willtmakinen78/weatherclock/pics/IMG_20200605_103530.jpg

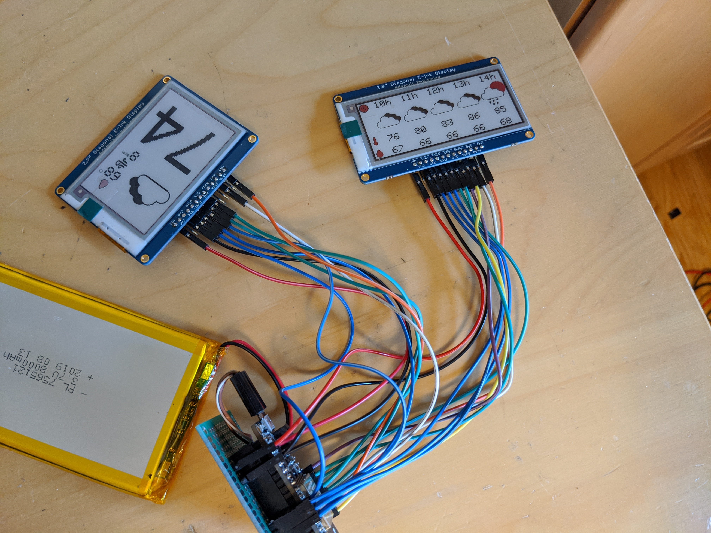
pics/IMG_20200605_103530.jpg
