willtmakinen78/weatherclock/pics/IMG_20210827_170739.jpg

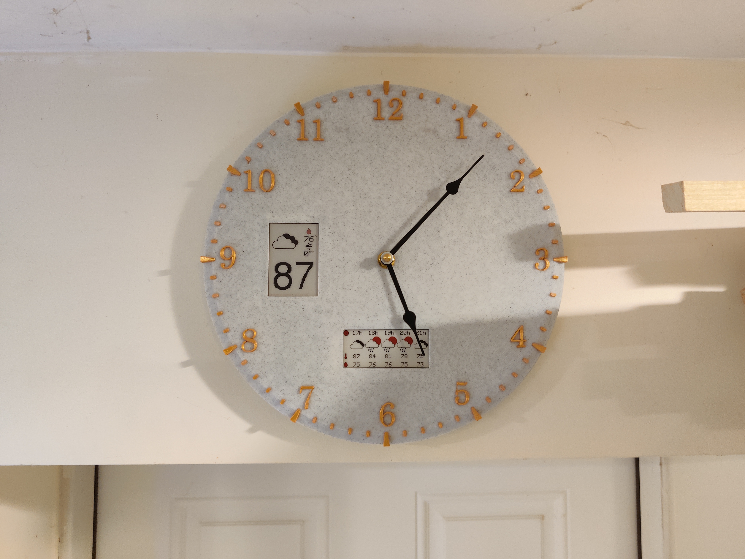
pics/IMG_20210827_170739.jpg
