willtmakinen78/weatherclock/pics/IMG_20210827_170756.jpg

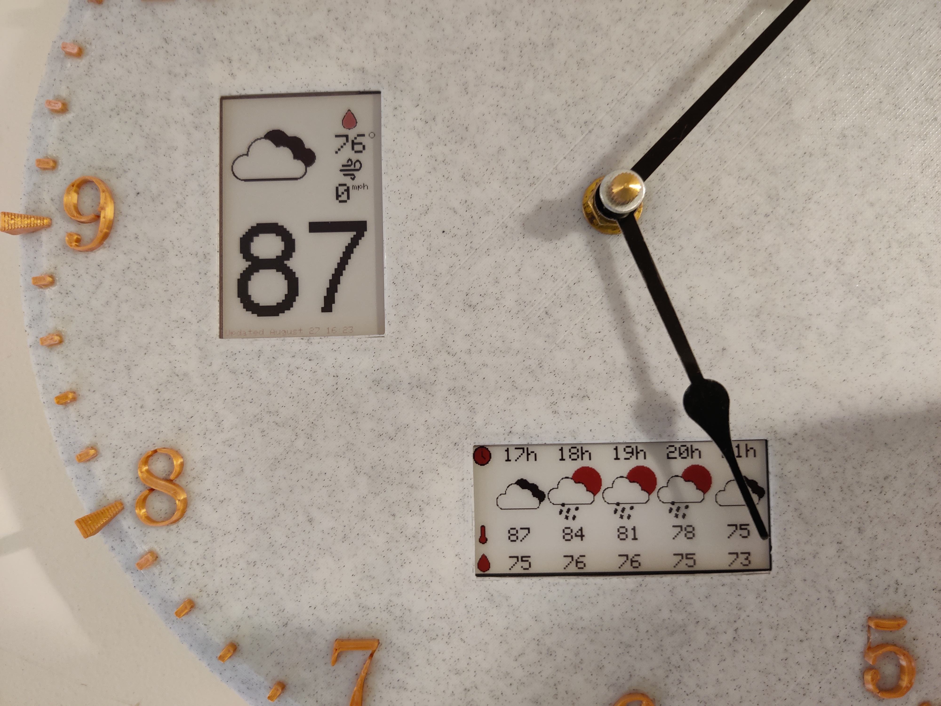
pics/IMG_20210827_170756.jpg
