willtmakinen78/weatherclock/pics/IMG_20210827_170835.jpg

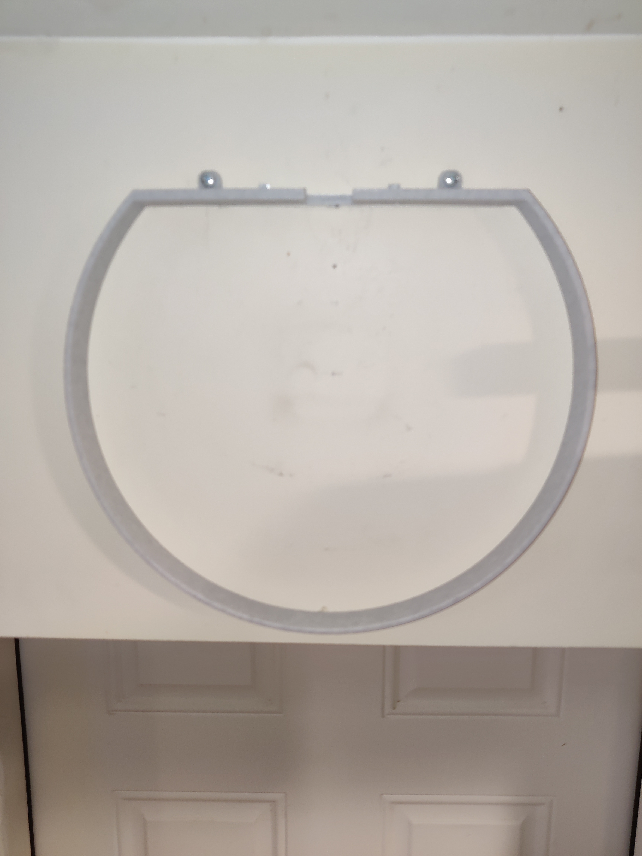
pics/IMG_20210827_170835.jpg
