willtmakinen78/weatherclock/pics/IMG_20210827_170838.jpg

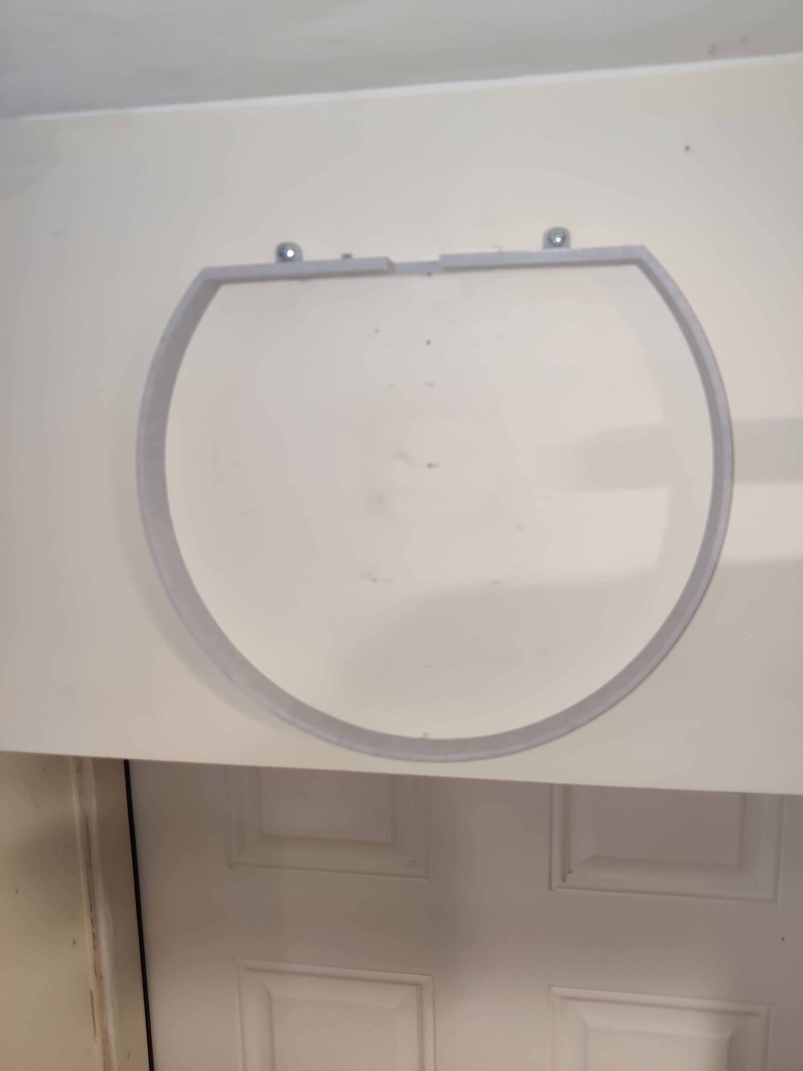
pics/IMG_20210827_170838.jpg
