willtmakinen78/weatherclock/pics/IMG_20210827_170912.jpg

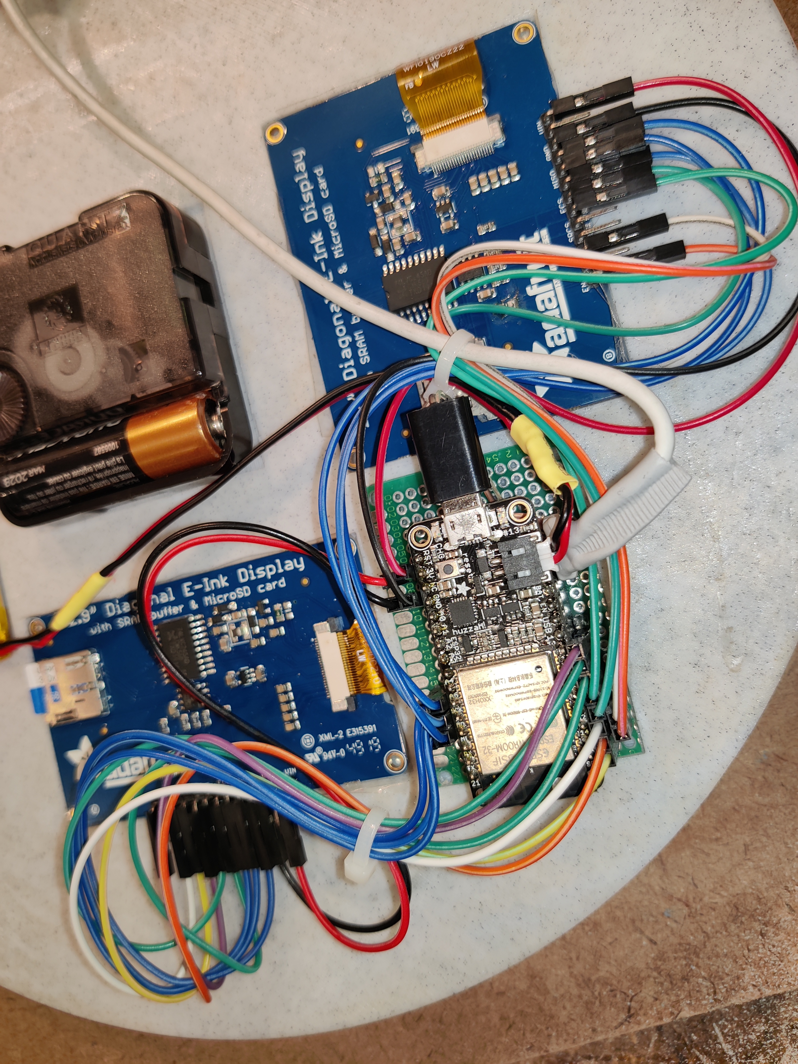
pics/IMG_20210827_170912.jpg
