willtmakinen78/weatherclock/cad/Numbers/1_1.stl

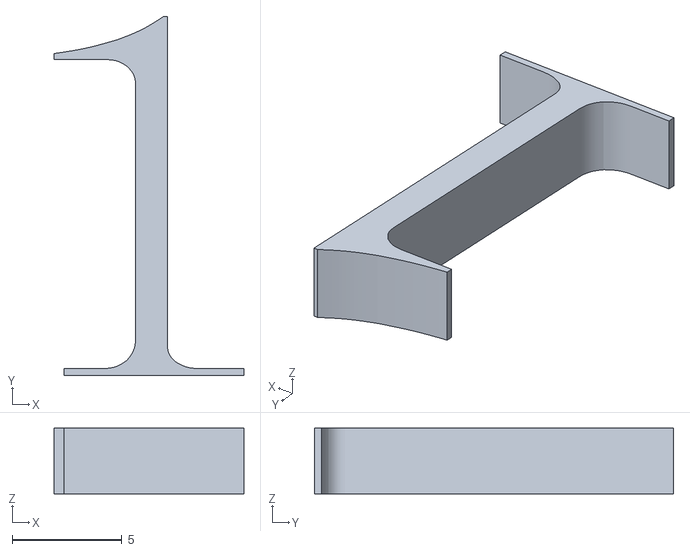
[picture p46: CAD file, 2021-09-05]
cad/Numbers/1_1.stl
8.63 x 16.3 x 3.00
