willtmakinen78/weatherclock/cad/Numbers/4.stl

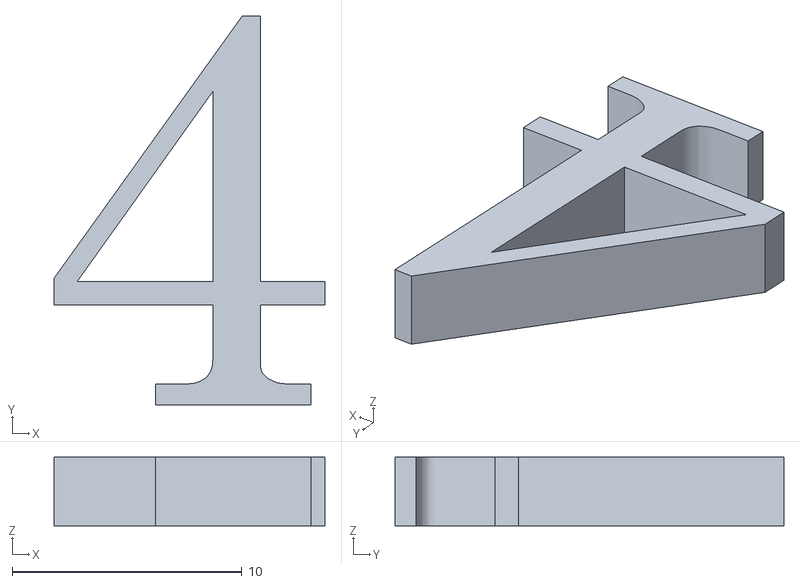
[picture p47: CAD file, 2021-09-05]
cad/Numbers/4.stl
11.8 x 16.9 x 3.00
