willtmakinen78/weatherclock/cad/Numbers/2.stl

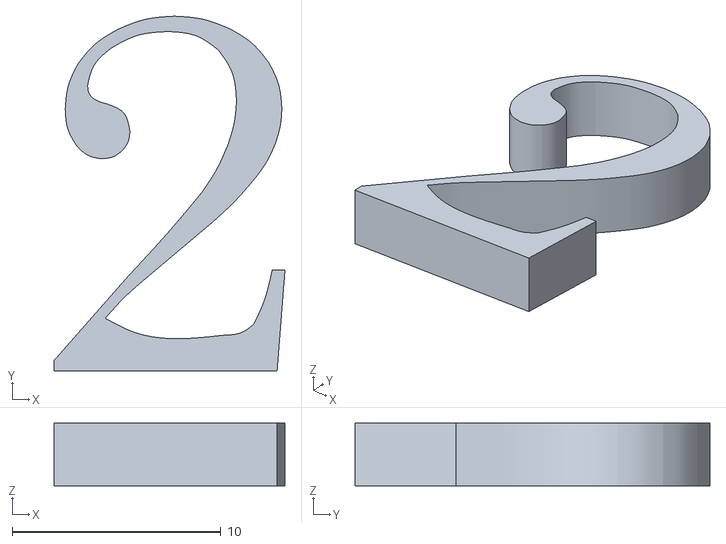
[picture p48: CAD file, 2021-09-05]
cad/Numbers/2.stl
11.1 x 17.0 x 3.00
