willtmakinen78/weatherclock/cad/Numbers/1_2.stl

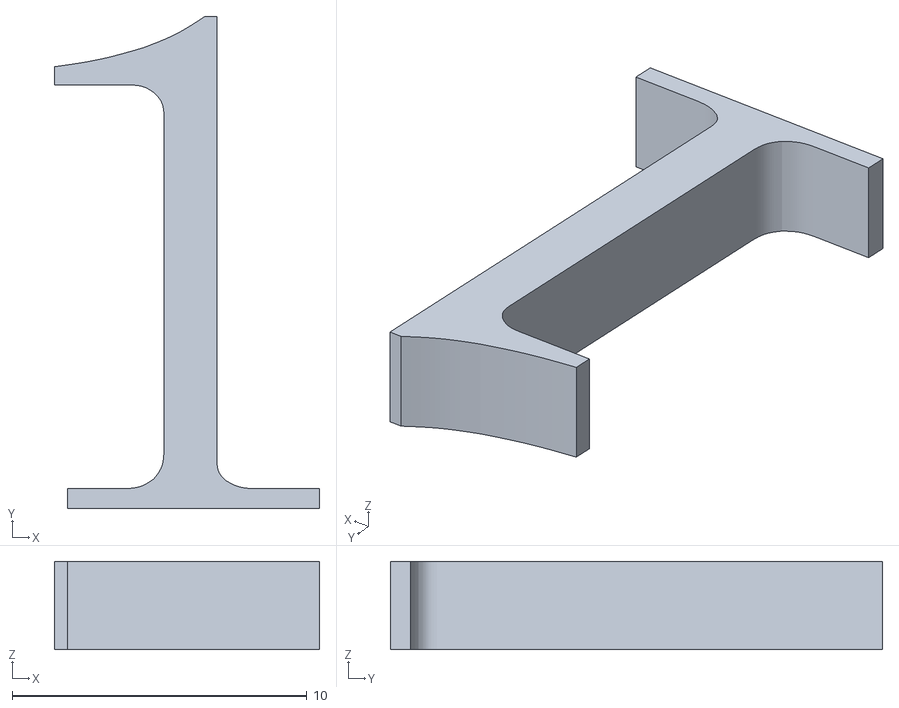
[picture p49: CAD file, 2021-09-05]
cad/Numbers/1_2.stl
8.99 x 16.7 x 3.00
